schult/anglo-midi/Schematic.kicad_sch

## KiCad design Schematic.kicad_sch (2022-08-20)

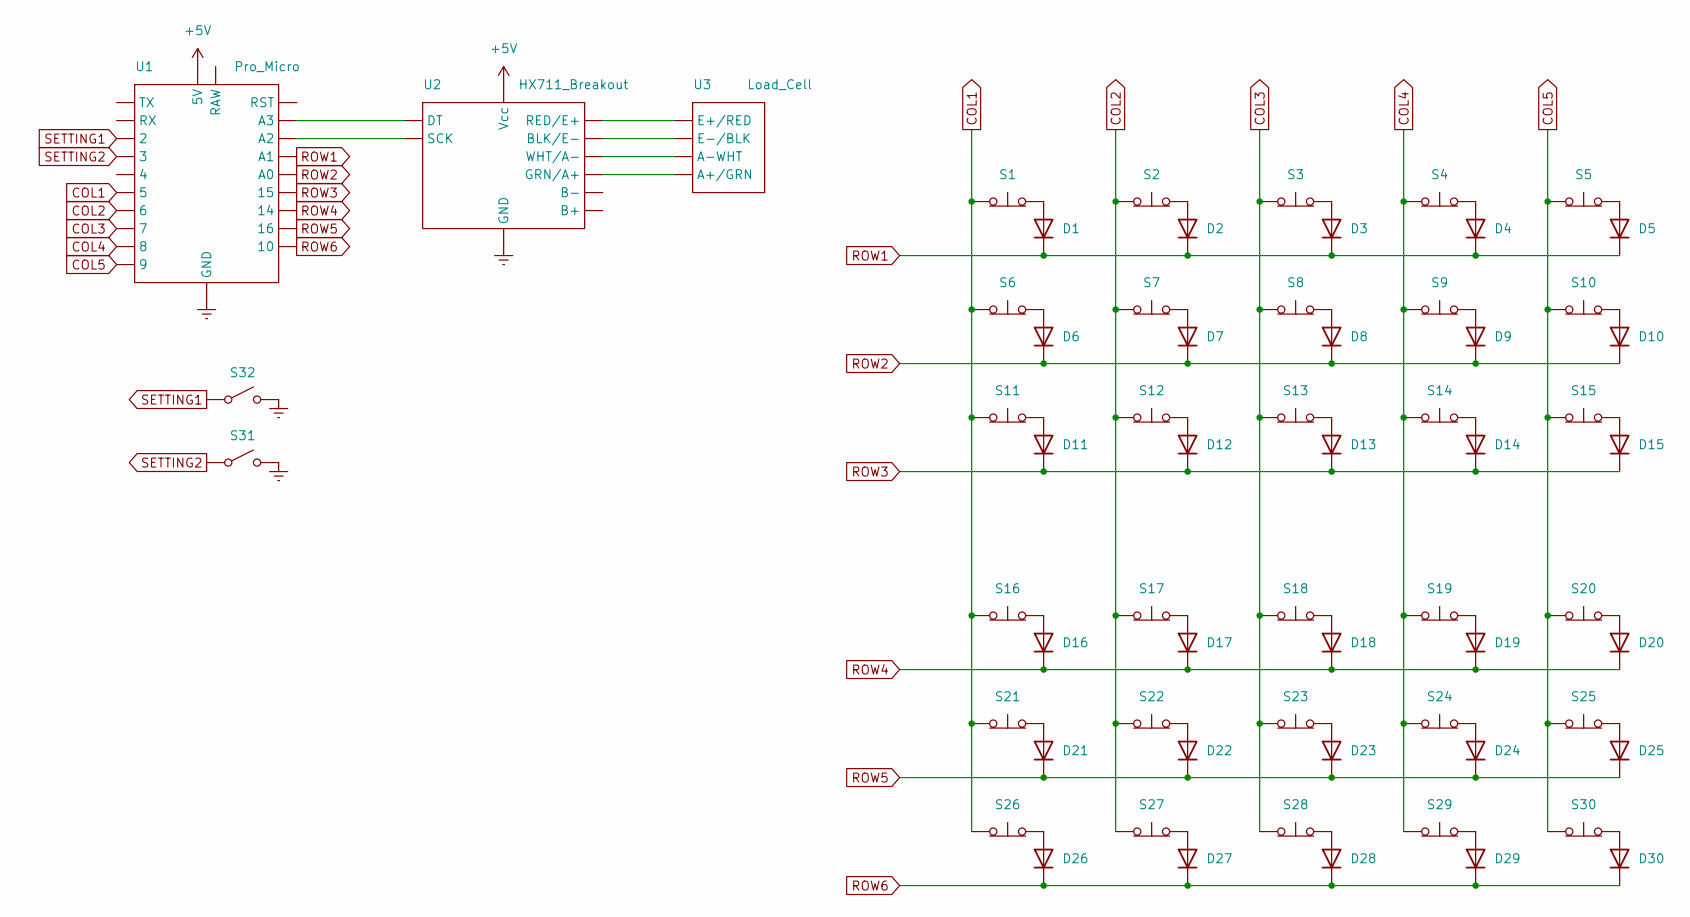
[picture p4: schematic Schematic.kicad_sch]

Parts:
D1, D2, D3, D4, D5, D6, D7, D8, D9, D10, D11, D12, D13, D14, D15, D16, D17, D18, D19, D20, D21, D22, D23, D24, D25, D26, D27, D28, D29, D30: 1N4148; D_DO-35_SOD27_P7.62mm_Horizontal
S1, S2, S3, S4, S5, S6, S7, S8, S9, S10, S11, S12, S13, S14, S15, S16, S17, S18, S19, S20, S21, S22, S23, S24, S25, S26, S27, S28, S29, S30: SW_Push_Open
S31, S32: SW_SPST
U1: Pro_Micro
U2: HX711_Breakout
U3: Load_Cell

Connections:
COL1: S1.1 (A), S6.1 (A), S11.1 (A), S16.1 (A), S21.1 (A), S26.1 (A), U1.5
COL2: S2.1 (A), S7.1 (A), S12.1 (A), S17.1 (A), S22.1 (A), S27.1 (A), U1.6
COL3: S3.1 (A), S8.1 (A), S13.1 (A), S18.1 (A), S23.1 (A), S28.1 (A), U1.7
COL4: S4.1 (A), S9.1 (A), S14.1 (A), S19.1 (A), S24.1 (A), S29.1 (A), U1.8
COL5: S5.1 (A), S10.1 (A), S15.1 (A), S20.1 (A), S25.1 (A), S30.1 (A), U1.9
unnamed: D1.2 (A), S1.2 (B)
unnamed: D2.2 (A), S2.2 (B)
unnamed: D3.2 (A), S3.2 (B)
unnamed: D4.2 (A), S4.2 (B)
unnamed: D5.2 (A), S5.2 (B)
unnamed: D6.2 (A), S6.2 (B)
unnamed: D7.2 (A), S7.2 (B)
unnamed: D8.2 (A), S8.2 (B)
unnamed: D9.2 (A), S9.2 (B)
unnamed: D10.2 (A), S10.2 (B)
unnamed: D11.2 (A), S11.2 (B)
unnamed: D12.2 (A), S12.2 (B)
unnamed: D13.2 (A), S13.2 (B)
unnamed: D14.2 (A), S14.2 (B)
unnamed: D15.2 (A), S15.2 (B)
unnamed: D16.2 (A), S16.2 (B)
unnamed: D17.2 (A), S17.2 (B)
unnamed: D18.2 (A), S18.2 (B)
unnamed: D19.2 (A), S19.2 (B)
unnamed: D20.2 (A), S20.2 (B)
unnamed: D21.2 (A), S21.2 (B)
unnamed: D22.2 (A), S22.2 (B)
unnamed: D23.2 (A), S23.2 (B)
unnamed: D24.2 (A), S24.2 (B)
unnamed: D25.2 (A), S25.2 (B)
unnamed: D26.2 (A), S26.2 (B)
unnamed: D27.2 (A), S27.2 (B)
unnamed: D28.2 (A), S28.2 (B)
unnamed: D29.2 (A), S29.2 (B)
unnamed: D30.2 (A), S30.2 (B)
unnamed: U1.A2, U2. (GND)
unnamed: U1.A3, U2.DT
unnamed: U2.A+ (GRN/A+), U3.
unnamed: U2.A- (WHT/A-), U3.
unnamed: U2.E+ (RED/E+), U3.
unnamed: U2.E- (BLK/E-), U3.
ROW1: D1.1 (K), D2.1 (K), D3.1 (K), D4.1 (K), D5.1 (K), U1.A1
ROW2: D6.1 (K), D7.1 (K), D8.1 (K), D9.1 (K), D10.1 (K), U1.A0
ROW3: D11.1 (K), D12.1 (K), D13.1 (K), D14.1 (K), D15.1 (K), U1.15
ROW4: D16.1 (K), D17.1 (K), D18.1 (K), D19.1 (K), D20.1 (K), U1.14
ROW5: D21.1 (K), D22.1 (K), D23.1 (K), D24.1 (K), D25.1 (K), U1.16
ROW6: D26.1 (K), D27.1 (K), D28.1 (K), D29.1 (K), D30.1 (K), U1.10
SETTING1: S32.1 (A), U1.2
SETTING2: S31.1 (A), U1.3
